jmacarthur/millihertz/scad/newbuild/generated_cams.scad

module moverCam() { 
difference () { 
linear_extrude (height=5) polygon( points=[[34.00000,0.00000],[33.87062,2.96330],[33.48346,5.90404],[32.84148,8.79985],[31.94955,11.62868],[30.81446,14.36902],[29.44486,17.00000],[34.40439,24.09021],[38.30222,32.13938],[34.97822,34.97822],[31.45374,37.48511],[27.76110,39.64696],[23.93333,41.45375],[20.00393,42.89857],[16.00654,43.97761],[11.97469,44.69017],[7.94151,45.03854],[3.93944,45.02800],[0.00000,44.66667],[-3.84647,43.96539],[-7.57106,42.93762],[-11.14647,41.59921],[-14.54726,39.96826],[-17.74997,38.06493],[-20.73333,35.91119],[-23.47840,33.53062],[-25.96862,30.94820],[-28.18999,28.18999],[-30.13108,25.28298],[-31.78310,22.25477],[-33.13991,19.13333],[-34.19801,15.94680],[-34.95657,12.72315],[-35.41728,9.49003],[-35.58439,6.27449],[-35.46453,3.10274],[-35.06667,0.00000],[-34.40192,-3.00978],[-33.48346,-5.90404],[-32.84148,-8.79985],[-31.94955,-11.62868],[-30.81446,-14.36902],[-29.44486,-17.00000],[-27.85117,-19.50160],[-26.04551,-21.85478],[-24.04163,-24.04163],[-21.85478,-26.04551],[-19.50160,-27.85117],[-17.00000,-29.44486],[-14.36902,-30.81446],[-11.62868,-31.94955],[-8.79985,-32.84148],[-5.90404,-33.48346],[-2.96330,-33.87062],[-0.00000,-34.00000],[2.96330,-33.87062],[5.90404,-33.48346],[8.79985,-32.84148],[11.62868,-31.94955],[14.36902,-30.81446],[17.00000,-29.44486],[19.50160,-27.85117],[21.85478,-26.04551],[24.04163,-24.04163],[26.04551,-21.85478],[27.85117,-19.50160],[29.44486,-17.00000],[30.81446,-14.36902],[31.94955,-11.62868],[32.84148,-8.79985],[33.48346,-5.90404],[33.87062,-2.96330],], 
paths = [[0,1,2,3,4,5,6,7,8,9,10,11,12,13,14,15,16,17,18,19,20,21,22,23,24,25,26,27,28,29,30,31,32,33,34,35,36,37,38,39,40,41,42,43,44,45,46,47,48,49,50,51,52,53,54,55,56,57,58,59,60,61,62,63,64,65,66,67,68,69,70,71, 0]] );
translate([-boxWidth/2,-boxWidth/2,-1]) cube(size=[boxWidth,boxWidth,10]);
translate([-10,0,-1]) cylinder(r=1.5,h=10);
translate([10,0,-1]) cylinder(r=1.5,h=10);
}
}
module lifterCam() { 
difference () { 
linear_extrude (height=5) polygon( points=[[38.00000,0.00000],[38.51953,3.37002],[38.73577,6.83016],[38.63703,10.35276],[38.21417,13.90882],[37.46072,17.46822],[36.37307,21.00000],[34.61808,24.23984],[32.57354,27.33245],[30.25187,30.25187],[27.66781,32.97322],[24.83835,35.47285],[21.78261,37.72858],[18.52170,39.71992],[15.07863,41.42819],[11.47806,42.83671],[7.74622,43.93099],[3.91064,44.69882],[0.00000,45.13043],[-3.95611,45.21858],[-7.92742,44.95861],[-11.88317,44.34859],[-15.79241,43.38929],[-19.62419,42.08421],[-23.34783,40.43962],[-26.93315,38.46453],[-30.35075,36.17062],[-33.57220,33.57220],[-36.57030,30.68612],[-39.31930,27.53167],[-41.79514,24.13043],[-43.97563,20.50617],[-45.84066,16.68463],[-47.37236,12.69339],[-48.55530,8.56161],[-49.37661,4.31989],[-49.82609,0.00000],[-49.89636,-4.36537],[-49.58293,-8.74281],[-48.88425,-13.09849],[-47.80176,-17.39842],[-46.33991,-21.60866],[-44.50618,-25.69565],[-42.31098,-29.62647],[-39.76770,-33.36906],[-36.89253,-36.89253],[-33.70443,-40.16737],[-30.22498,-43.16575],[-26.47826,-45.86169],[-22.49064,-48.23134],[-18.29064,-50.25313],[-13.90871,-51.90801],[-9.37700,-53.17962],[-4.63669,-52.99756],[-0.00000,-52.40000],[4.49724,-51.40365],[8.82133,-50.02823],[12.94095,-48.29629],[16.82739,-46.23288],[20.45472,-43.86530],[23.80000,-41.22281],[26.84338,-38.33632],[29.56823,-35.23804],[31.96123,-31.96123],[34.01237,-28.53977],[35.71503,-25.00793],[37.06589,-21.40000],[38.06493,-17.74997],[38.71534,-14.09123],[39.02340,-10.45629],[38.99839,-6.87647],[38.65235,-3.38164],], 
paths = [[0,1,2,3,4,5,6,7,8,9,10,11,12,13,14,15,16,17,18,19,20,21,22,23,24,25,26,27,28,29,30,31,32,33,34,35,36,37,38,39,40,41,42,43,44,45,46,47,48,49,50,51,52,53,54,55,56,57,58,59,60,61,62,63,64,65,66,67,68,69,70,71,0,1,2,3,4,5,6,7,8,9,10,11,12,13,14,15,16,17,18,19,20,21,22,23,24,25,26,27,28,29,30,31,32,33,34,35,36,37,38,39,40,41,42,43,44,45,46,47,48,49,50,51,52,53,54,55,56,57,58,59,60,61,62,63,64,65,66,67,68,69,70,71, 0]] );
translate([-boxWidth/2,-boxWidth/2,-1]) cube(size=[boxWidth,boxWidth,10]);
translate([-10,0,-1]) cylinder(r=1.5,h=10);
translate([10,0,-1]) cylinder(r=1.5,h=10);
}
}
module resetCam() { 
difference () { 
linear_extrude (height=5) polygon( points=[[42.00000,0.00000],[41.84018,3.66054],[41.36193,7.29322],[40.56888,10.87040],[39.46709,14.36485],[38.06493,17.74997],[36.37307,21.00000],[34.40439,24.09021],[32.17387,26.99708],[29.69848,29.69848],[26.99708,32.17387],[24.09021,34.40439],[21.00000,36.37307],[17.74997,38.06493],[14.36485,39.46709],[10.87040,40.56888],[7.29322,41.36193],[3.66054,41.84018],[0.00000,42.00000],[-3.66054,41.84018],[-7.29322,41.36193],[-10.87040,40.56888],[-14.36485,39.46709],[-17.74997,38.06493],[-21.00000,36.37307],[-24.09021,34.40439],[-26.99708,32.17387],[-29.69848,29.69848],[-32.17387,26.99708],[-34.40439,24.09021],[-36.37307,21.00000],[-38.06493,17.74997],[-39.46709,14.36485],[-40.56888,10.87040],[-41.36193,7.29322],[-41.84018,3.66054],[-42.00000,0.00000],[-41.84018,-3.66054],[-41.36193,-7.29322],[-40.56888,-10.87040],[-39.46709,-14.36485],[-38.06493,-17.74997],[-36.37307,-21.00000],[-34.40439,-24.09021],[-32.17387,-26.99708],[-29.69848,-29.69848],[-26.99708,-32.17387],[-24.09021,-34.40439],[-21.00000,-36.37307],[-17.74997,-38.06493],[-14.36485,-39.46709],[-10.87040,-40.56888],[-7.29322,-41.36193],[-3.66054,-41.84018],[-0.00000,-42.00000],[3.66054,-41.84018],[7.29322,-41.36193],[10.87040,-40.56888],[14.36485,-39.46709],[17.74997,-38.06493],[21.00000,-36.37307],[25.52415,-36.45227],[30.21102,-36.00409],[31.46625,-31.46625],[32.17387,-26.99708],[34.40439,-24.09021],[36.37307,-21.00000],[38.06493,-17.74997],[39.46709,-14.36485],[40.56888,-10.87040],[41.36193,-7.29322],[41.84018,-3.66054],], 
paths = [[0,1,2,3,4,5,6,7,8,9,10,11,12,13,14,15,16,17,18,19,20,21,22,23,24,25,26,27,28,29,30,31,32,33,34,35,36,37,38,39,40,41,42,43,44,45,46,47,48,49,50,51,52,53,54,55,56,57,58,59,60,61,62,63,64,65,66,67,68,69,70,71,0,1,2,3,4,5,6,7,8,9,10,11,12,13,14,15,16,17,18,19,20,21,22,23,24,25,26,27,28,29,30,31,32,33,34,35,36,37,38,39,40,41,42,43,44,45,46,47,48,49,50,51,52,53,54,55,56,57,58,59,60,61,62,63,64,65,66,67,68,69,70,71,0,1,2,3,4,5,6,7,8,9,10,11,12,13,14,15,16,17,18,19,20,21,22,23,24,25,26,27,28,29,30,31,32,33,34,35,36,37,38,39,40,41,42,43,44,45,46,47,48,49,50,51,52,53,54,55,56,57,58,59,60,61,62,63,64,65,66,67,68,69,70,71, 0]] );
translate([-boxWidth/2,-boxWidth/2,-1]) cube(size=[boxWidth,boxWidth,10]);
translate([-10,0,-1]) cylinder(r=1.5,h=10);
translate([10,0,-1]) cylinder(r=1.5,h=10);
}
}
module dirAmpCam() { 
difference () { 
linear_extrude (height=5) polygon( points=[[42.00000,0.00000],[41.84018,3.66054],[41.36193,7.29322],[40.56888,10.87040],[39.46709,14.36485],[38.06493,17.74997],[36.37307,21.00000],[34.40439,24.09021],[32.17387,26.99708],[29.69848,29.69848],[26.99708,32.17387],[24.09021,34.40439],[21.00000,36.37307],[17.74997,38.06493],[14.36485,39.46709],[10.87040,40.56888],[7.29322,41.36193],[3.66054,41.84018],[0.00000,42.00000],[-3.66054,41.84018],[-7.29322,41.36193],[-10.87040,40.56888],[-14.36485,39.46709],[-17.74997,38.06493],[-21.00000,36.37307],[-24.09021,34.40439],[-26.99708,32.17387],[-29.69848,29.69848],[-32.17387,26.99708],[-34.40439,24.09021],[-36.37307,21.00000],[-38.06493,17.74997],[-39.46709,14.36485],[-40.56888,10.87040],[-41.36193,7.29322],[-41.84018,3.66054],[-42.00000,0.00000],[-41.84018,-3.66054],[-41.36193,-7.29322],[-40.56888,-10.87040],[-39.46709,-14.36485],[-38.63137,-18.01410],[-37.45560,-21.62500],[-35.94030,-25.16567],[-34.08898,-28.60405],[-31.46625,-31.46625],[-28.60405,-34.08898],[-25.52415,-36.45227],[-22.25000,-38.53813],[-18.80651,-40.33070],[-15.21990,-41.81632],[-11.51745,-42.98370],[-7.72734,-43.82395],[-3.87843,-44.33066],[-0.00000,-44.50000],[3.87843,-44.33066],[7.72734,-43.82395],[11.51745,-42.98370],[15.21990,-41.81632],[18.80651,-40.33070],[22.25000,-38.53813],[25.52415,-36.45227],[28.60405,-34.08898],[31.46625,-31.46625],[34.08898,-28.60405],[36.45227,-25.52415],[38.53813,-22.25000],[40.33070,-18.80651],[41.81632,-15.21990],[42.38000,-11.35569],[42.59294,-7.51028],[42.46280,-3.71501],], 
paths = [[0,1,2,3,4,5,6,7,8,9,10,11,12,13,14,15,16,17,18,19,20,21,22,23,24,25,26,27,28,29,30,31,32,33,34,35,36,37,38,39,40,41,42,43,44,45,46,47,48,49,50,51,52,53,54,55,56,57,58,59,60,61,62,63,64,65,66,67,68,69,70,71,0,1,2,3,4,5,6,7,8,9,10,11,12,13,14,15,16,17,18,19,20,21,22,23,24,25,26,27,28,29,30,31,32,33,34,35,36,37,38,39,40,41,42,43,44,45,46,47,48,49,50,51,52,53,54,55,56,57,58,59,60,61,62,63,64,65,66,67,68,69,70,71,0,1,2,3,4,5,6,7,8,9,10,11,12,13,14,15,16,17,18,19,20,21,22,23,24,25,26,27,28,29,30,31,32,33,34,35,36,37,38,39,40,41,42,43,44,45,46,47,48,49,50,51,52,53,54,55,56,57,58,59,60,61,62,63,64,65,66,67,68,69,70,71,0,1,2,3,4,5,6,7,8,9,10,11,12,13,14,15,16,17,18,19,20,21,22,23,24,25,26,27,28,29,30,31,32,33,34,35,36,37,38,39,40,41,42,43,44,45,46,47,48,49,50,51,52,53,54,55,56,57,58,59,60,61,62,63,64,65,66,67,68,69,70,71, 0]] );
translate([-boxWidth/2,-boxWidth/2,-1]) cube(size=[boxWidth,boxWidth,10]);
translate([-10,0,-1]) cylinder(r=1.5,h=10);
translate([10,0,-1]) cylinder(r=1.5,h=10);
}
}
