jmacarthur/millihertz/scad/ram/globs.scad

column_x_spacing = 24;
row_y_spacing = 20;
ballBearingDiameter = 6;
rows = 8;
cols = 8;
column_travel = 13;
