jmacarthur/millihertz/scad/selector/globs.scad

thin = 0.1;
